OzSecICT/badge-crashandburn/hardware/kicad/OzSec2025-ESP32/images/dialpad.png

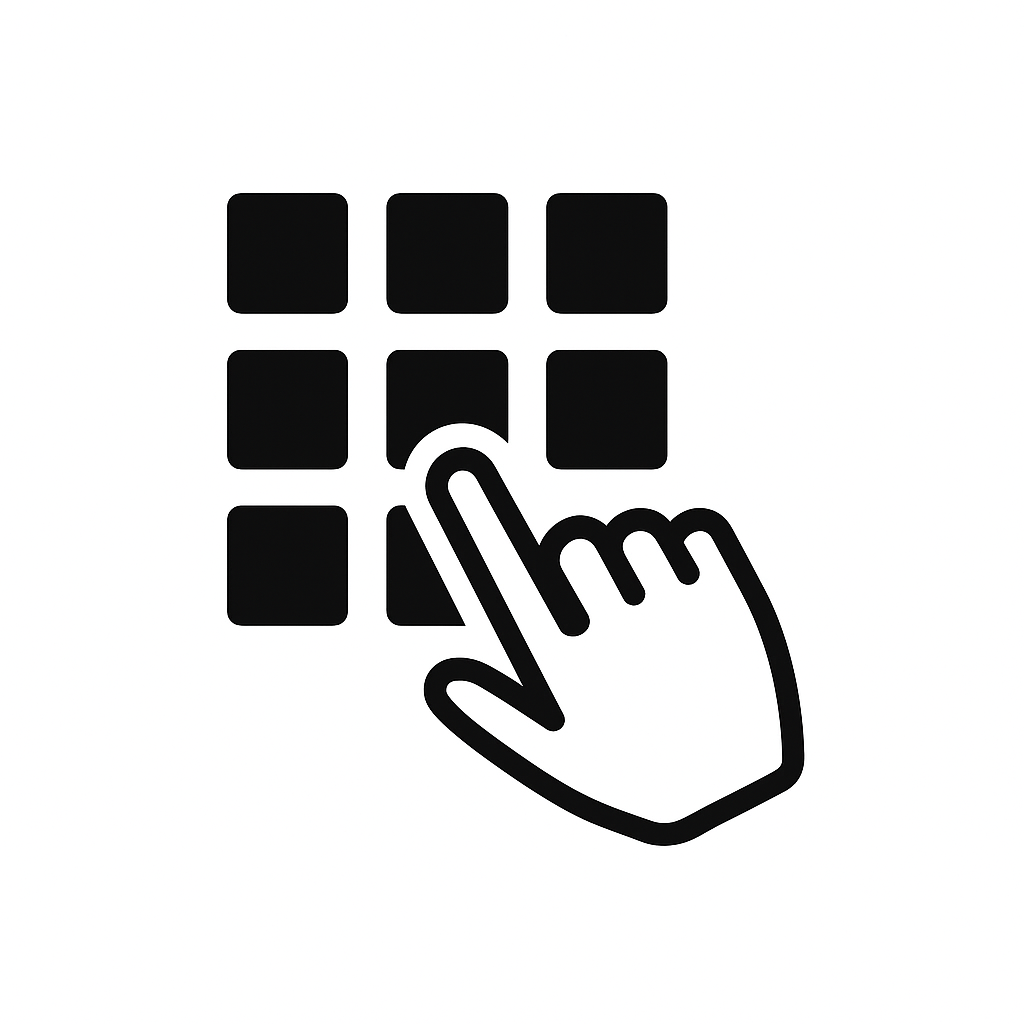
hardware/kicad/OzSec2025-ESP32/images/dialpad.png
