OzSecICT/badge-crashandburn/hardware/kicad/OzSec2025-ESP32/images/globe.png

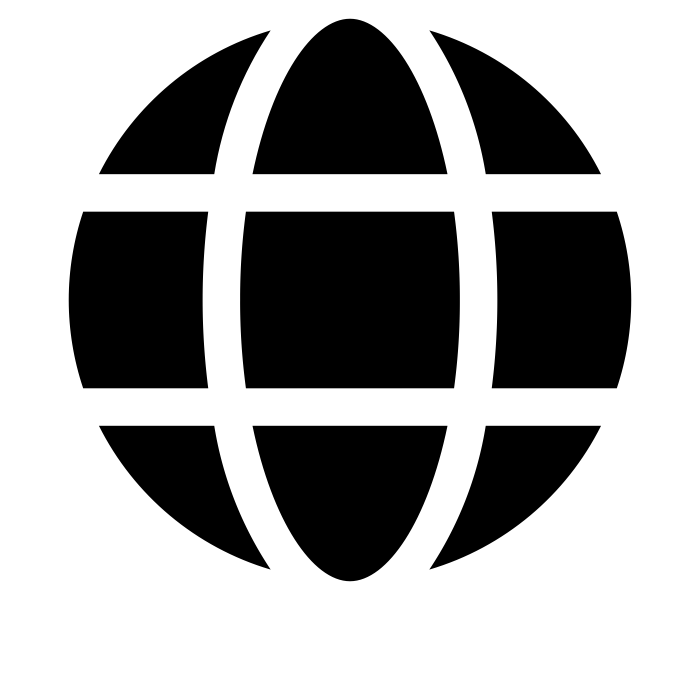
hardware/kicad/OzSec2025-ESP32/images/globe.png
