OzSecICT/badge-crashandburn/hardware/kicad/OzSec2025-ESP32/images/hackthecon_complete.jpg

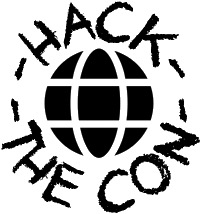
hardware/kicad/OzSec2025-ESP32/images/hackthecon_complete.jpg
