OzSecICT/badge-crashandburn/hardware/kicad/OzSec2025-ESP32/images/hertz.png

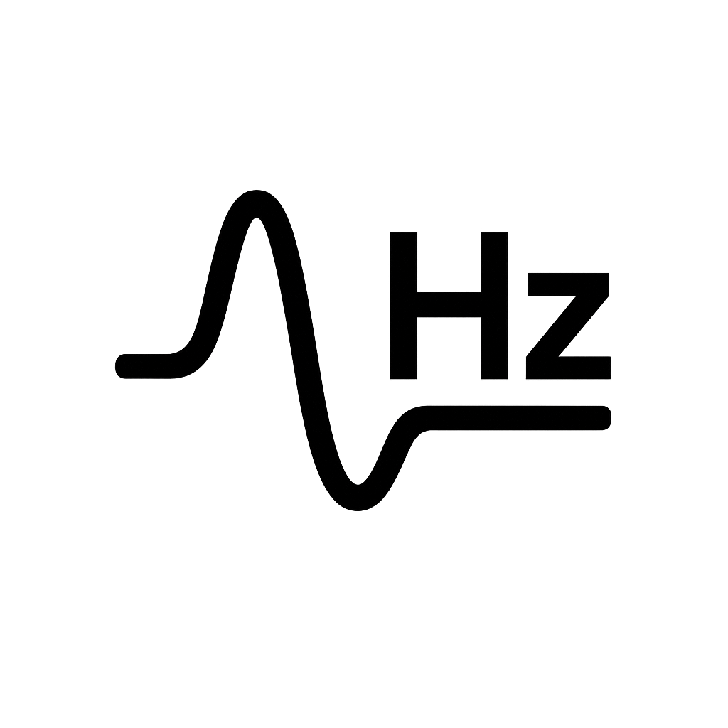
hardware/kicad/OzSec2025-ESP32/images/hertz.png
