OzSecICT/badge-crashandburn/hardware/kicad/OzSec2025-ESP32/images/hightop-sneaker.png

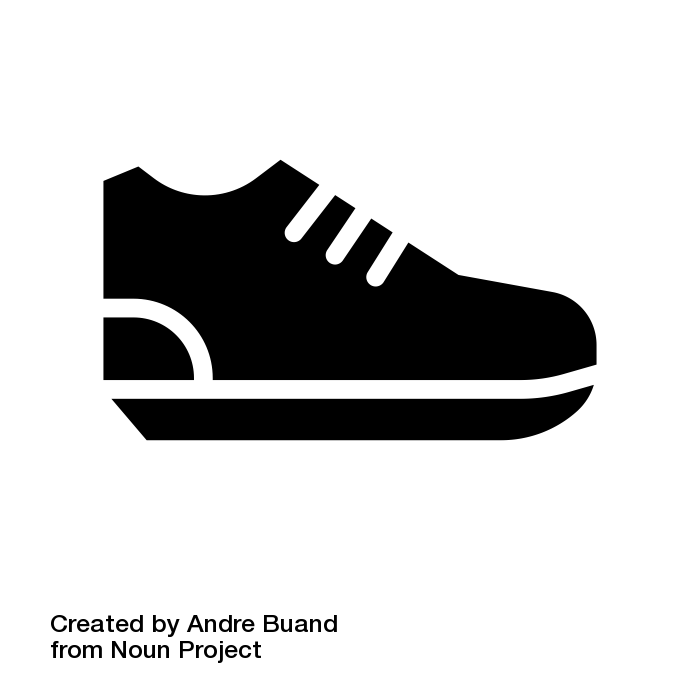
hardware/kicad/OzSec2025-ESP32/images/hightop-sneaker.png
