OzSecICT/badge-crashandburn/hardware/kicad/OzSec2025-ESP32/images/lowtop.png

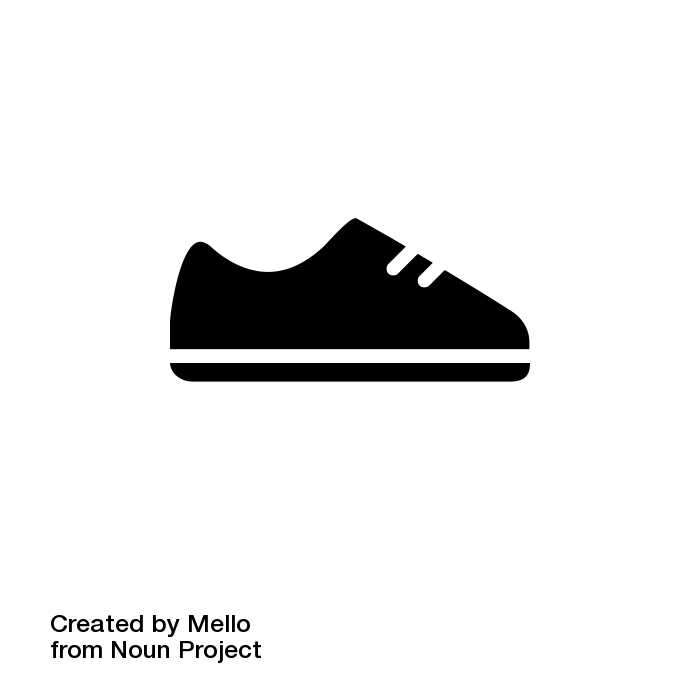
hardware/kicad/OzSec2025-ESP32/images/lowtop.png
