OzSecICT/badge-crashandburn/hardware/kicad/OzSec2025-ESP32/images/NumberPad.png

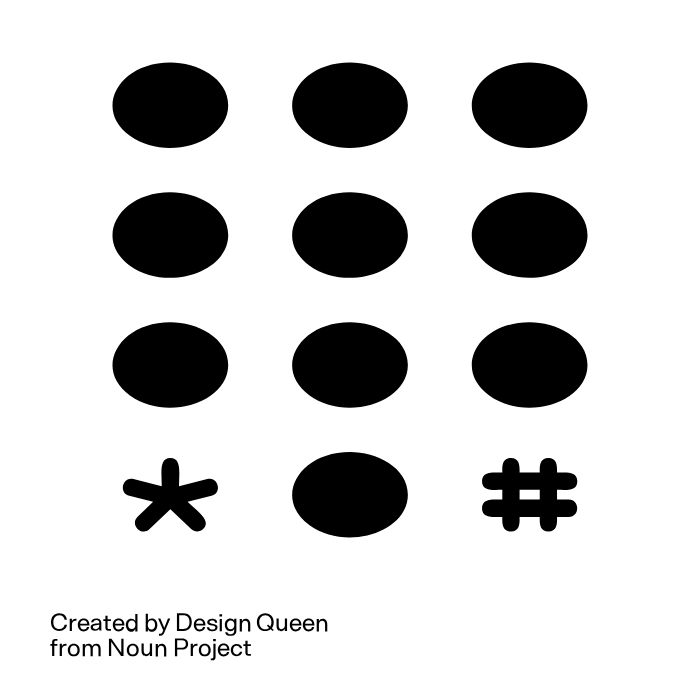
hardware/kicad/OzSec2025-ESP32/images/NumberPad.png
