OzSecICT/badge-crashandburn/hardware/kicad/OzSec2025-ESP32/images/paper.png

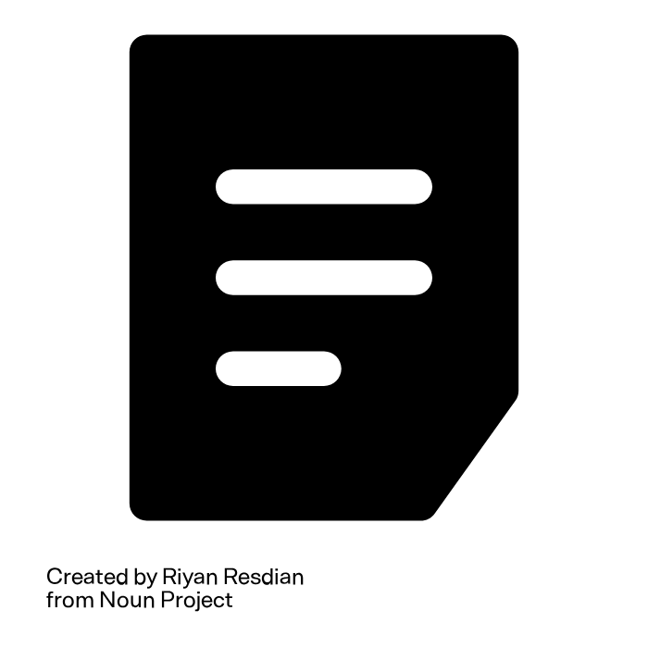
hardware/kicad/OzSec2025-ESP32/images/paper.png
