OzSecICT/badge-crashandburn/hardware/kicad/OzSec2025-ESP32/images/raffle-bonus.png

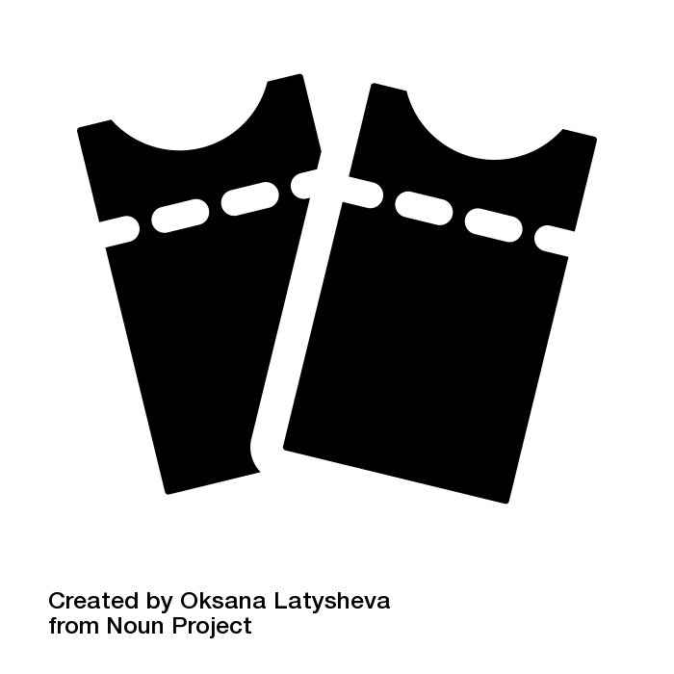
hardware/kicad/OzSec2025-ESP32/images/raffle-bonus.png
