OzSecICT/badge-crashandburn/hardware/kicad/OzSec2025-ESP32/images/Rendering_Blue.png

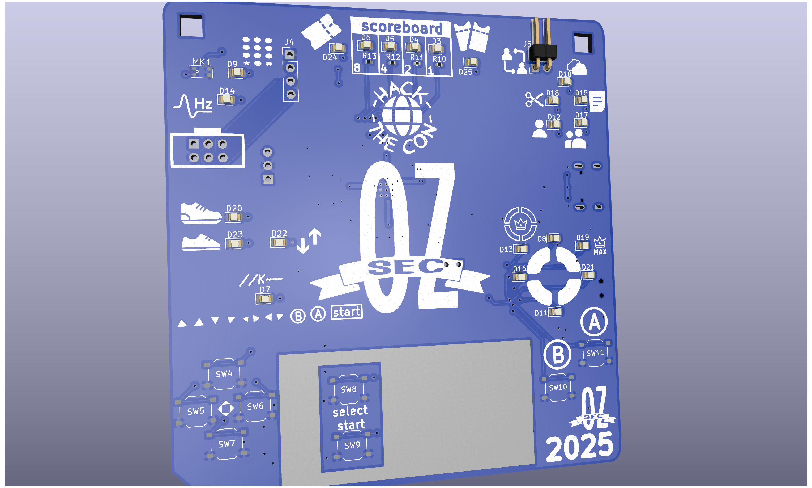
hardware/kicad/OzSec2025-ESP32/images/Rendering_Blue.png
