OzSecICT/badge-crashandburn/hardware/kicad/OzSec2025-ESP32/images/Rendering_Yellow.png

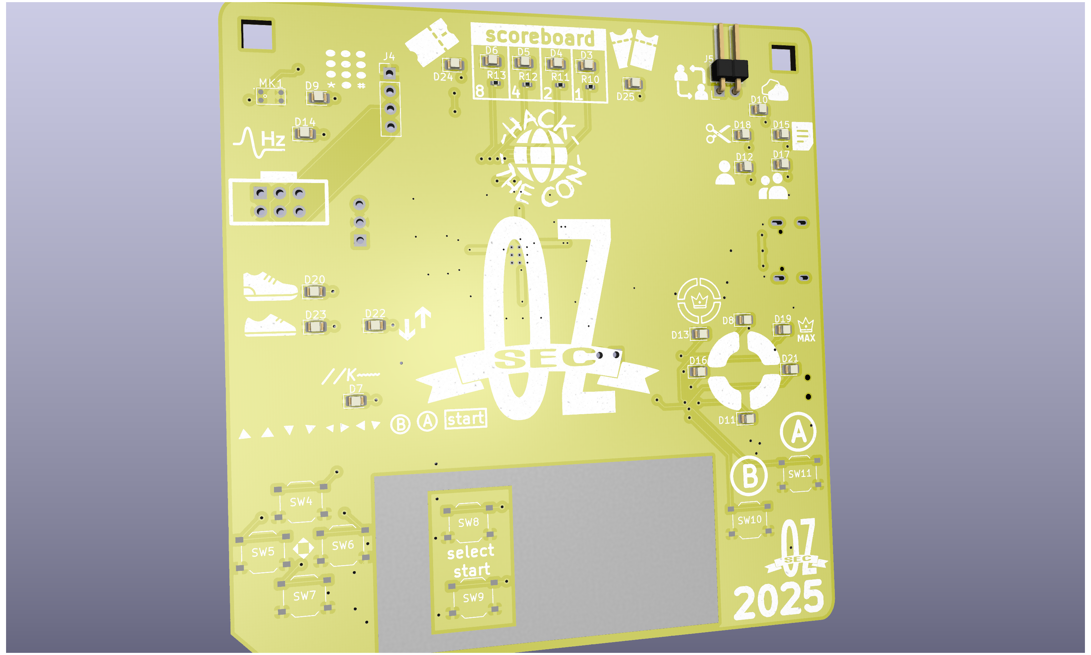
hardware/kicad/OzSec2025-ESP32/images/Rendering_Yellow.png
