OzSecICT/badge-crashandburn/hardware/kicad/OzSec2025-ESP32/images/rock.png

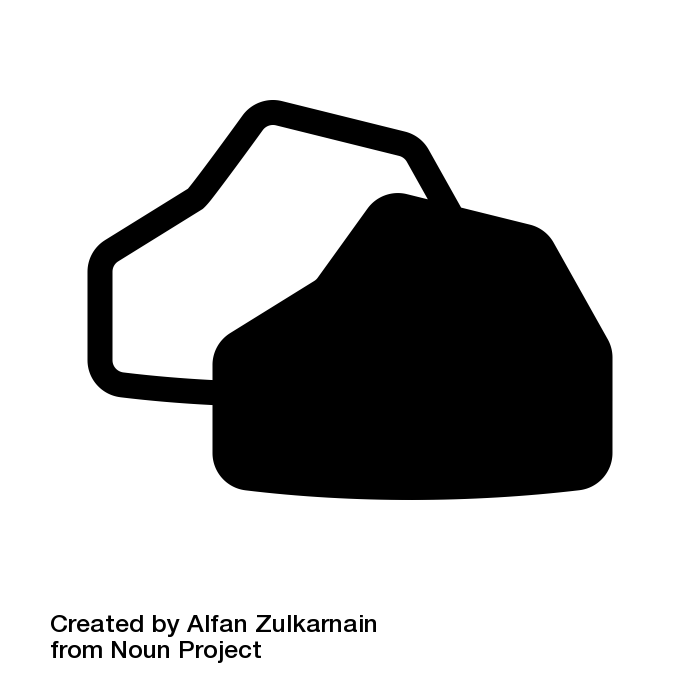
hardware/kicad/OzSec2025-ESP32/images/rock.png
