OzSecICT/badge-crashandburn/hardware/kicad/OzSec2025-ESP32/images/rps-multi.png

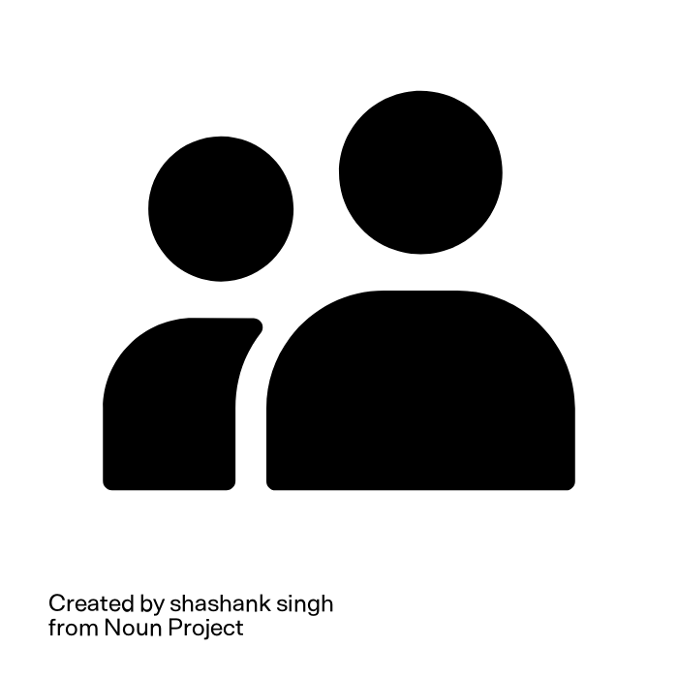
hardware/kicad/OzSec2025-ESP32/images/rps-multi.png
