OzSecICT/badge-crashandburn/hardware/kicad/OzSec2025-ESP32/images/scissors.png

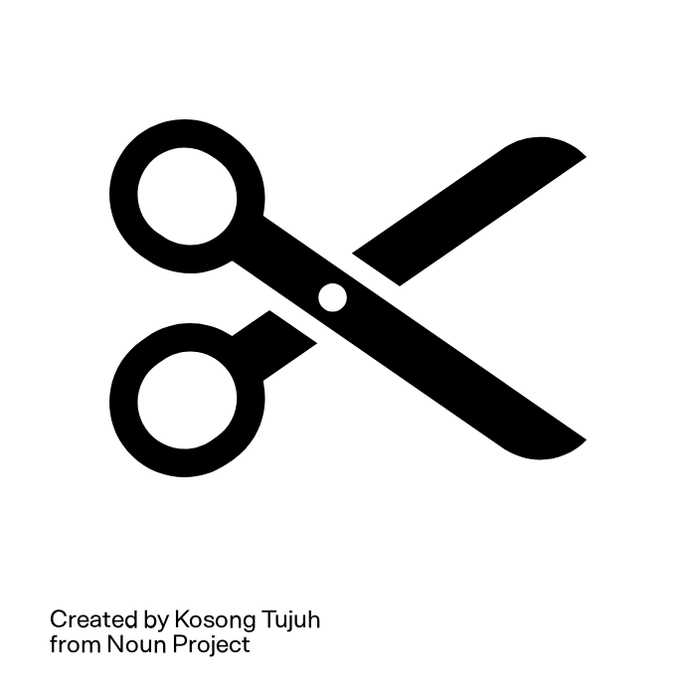
hardware/kicad/OzSec2025-ESP32/images/scissors.png
