OzSecICT/badge-crashandburn/hardware/kicad/OzSec2025-ESP32/images/simon.png

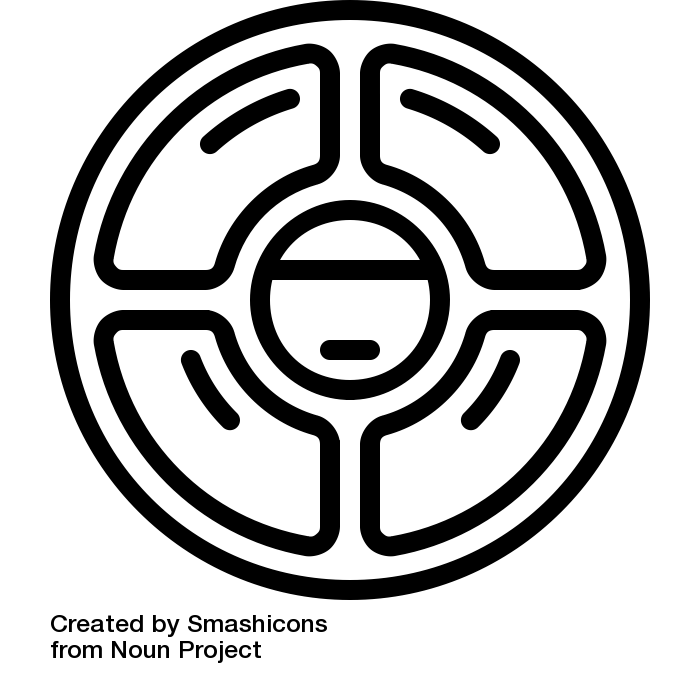
hardware/kicad/OzSec2025-ESP32/images/simon.png
