OzSecICT/badge-crashandburn/hardware/kicad/OzSec2025-ESP32/images/squiggle.png

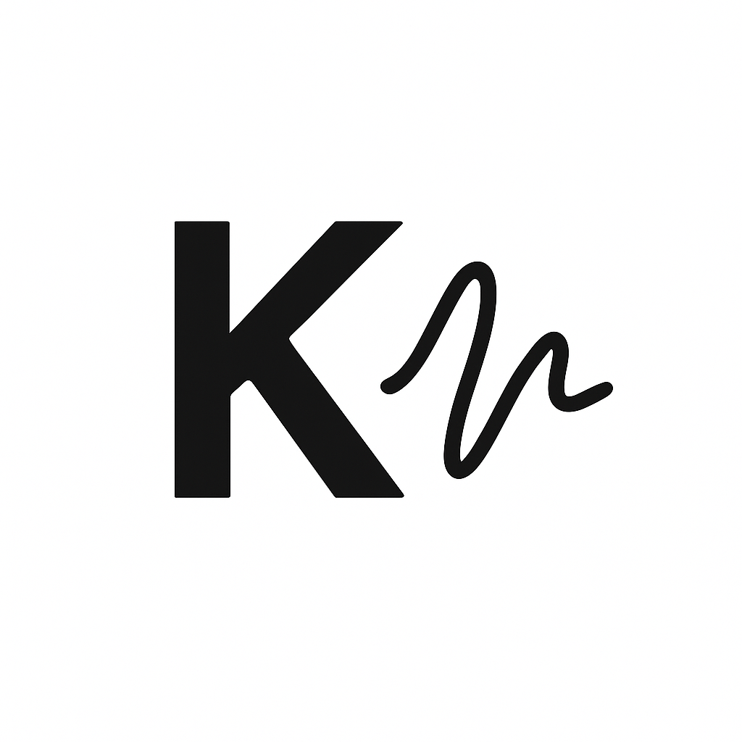
hardware/kicad/OzSec2025-ESP32/images/squiggle.png
