OzSecICT/badge-crashandburn/hardware/kicad/OzSec2025-ESP32/images/updown.png

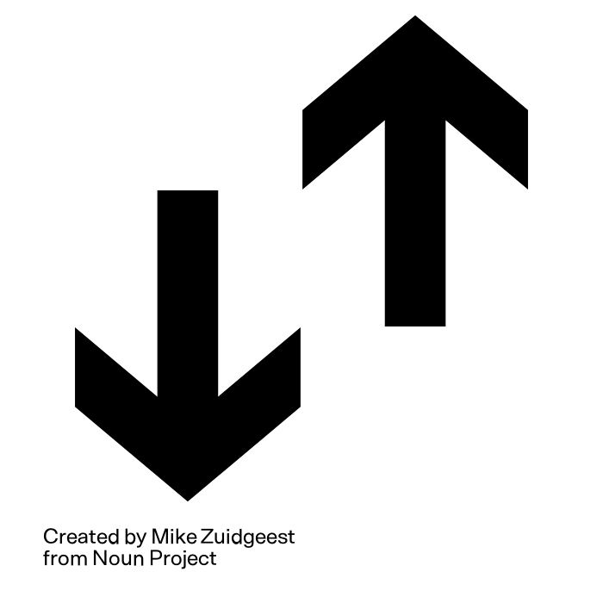
hardware/kicad/OzSec2025-ESP32/images/updown.png
