OzSecICT/badge-crashandburn/source/boot.py

"""
Boot Script

The `boot.py` script is executed on boot. It can be used for any one-time initialization tasks.
"""
import sys

print("Boot script running...")
sys.path.append("..")  # Add parent directory to import path
